AnnaMarburger/SketchingWithHardware/birdbooth_files/schaltplan.png

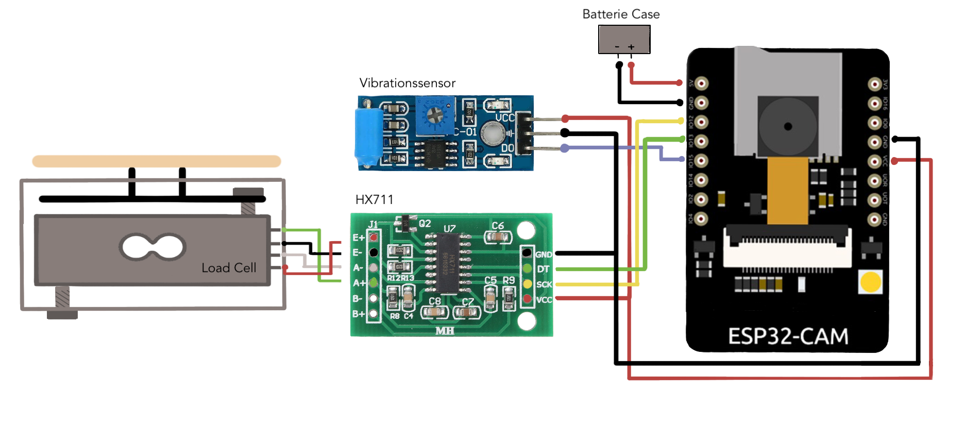
birdbooth_files/schaltplan.png
