AnnaMarburger/SketchingWithHardware/content/posts/media/infoschild.png

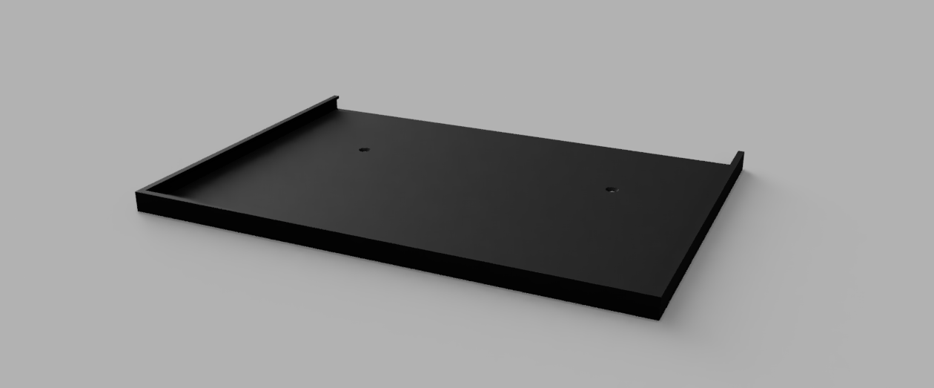
content/posts/media/infoschild.png
