AnnaMarburger/SketchingWithHardware/content/posts/media/lab4_qboydruck.jpeg

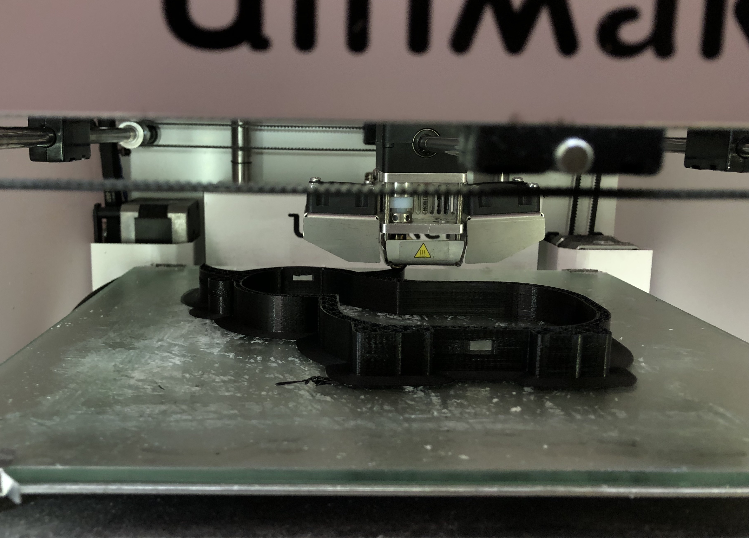
content/posts/media/lab4_qboydruck.jpeg
