AnnaMarburger/SketchingWithHardware/content/posts/media/mech_3gang_1.jpeg

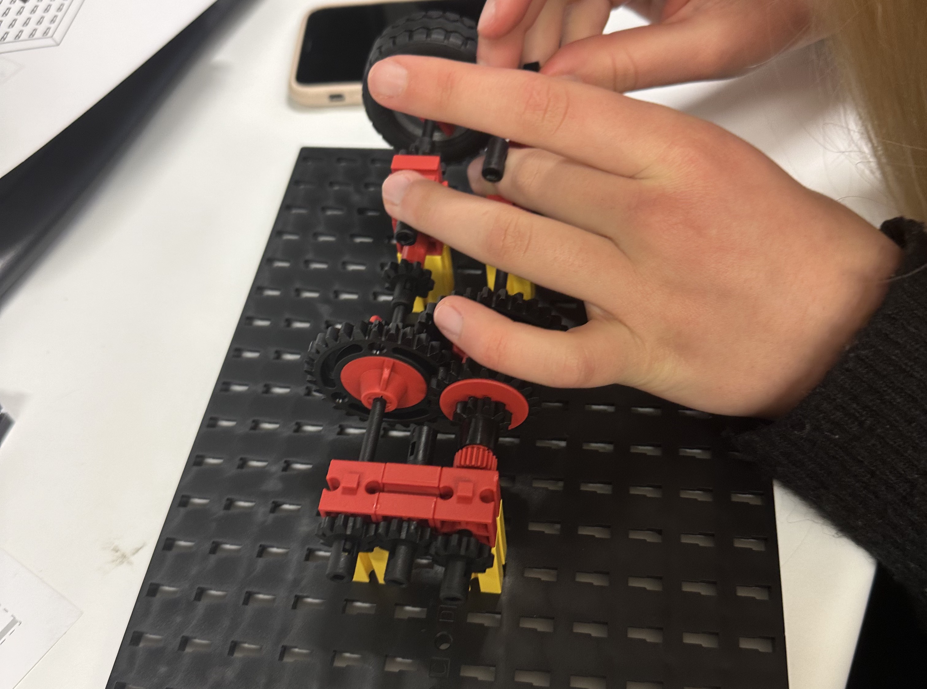
content/posts/media/mech_3gang_1.jpeg
