AnnaMarburger/SketchingWithHardware/content/posts/media/mech_getriebe.jpeg

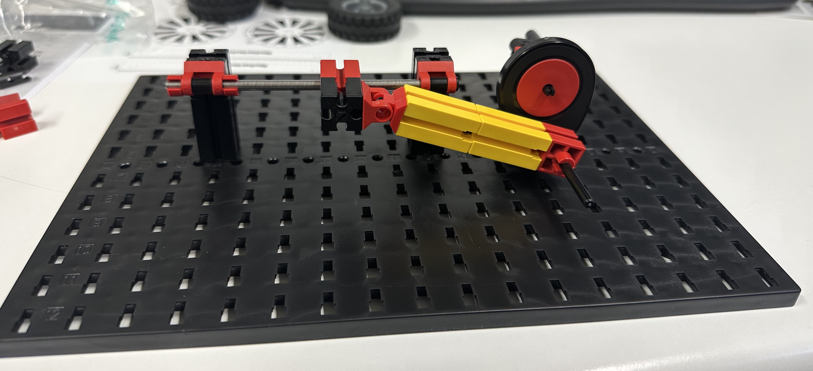
content/posts/media/mech_getriebe.jpeg
