AnnaMarburger/SketchingWithHardware/content/posts/media/mech_titel.jpeg

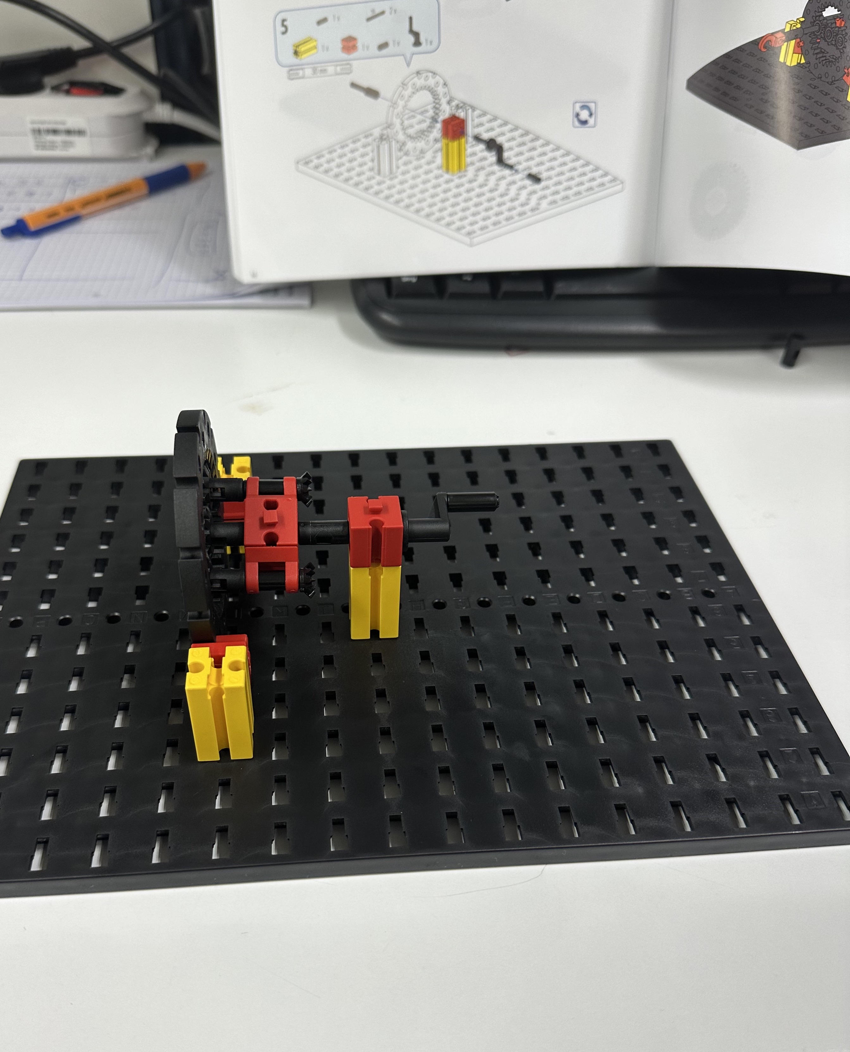
content/posts/media/mech_titel.jpeg
