AnnaMarburger/SketchingWithHardware/content/posts/media/projekt/ablaufdiagramm.png

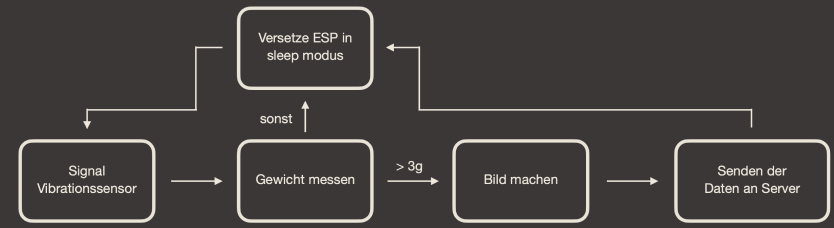
content/posts/media/projekt/ablaufdiagramm.png
