AnnaMarburger/SketchingWithHardware/content/posts/media/projekt/bauteile_gewichtssensor.jpeg

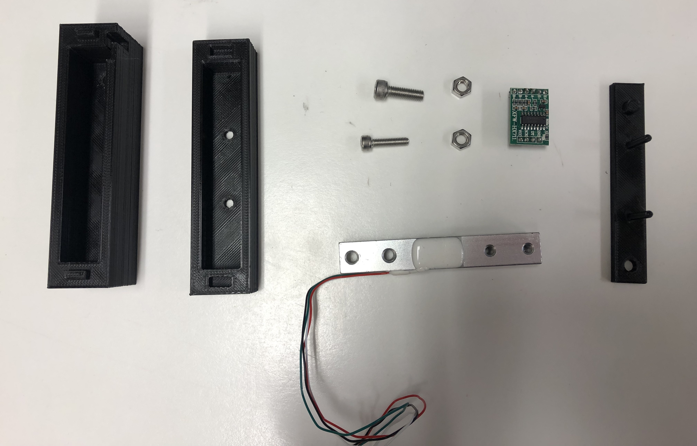
content/posts/media/projekt/bauteile_gewichtssensor.jpeg
