AnnaMarburger/SketchingWithHardware/content/posts/media/projekt/dachplatte.jpeg

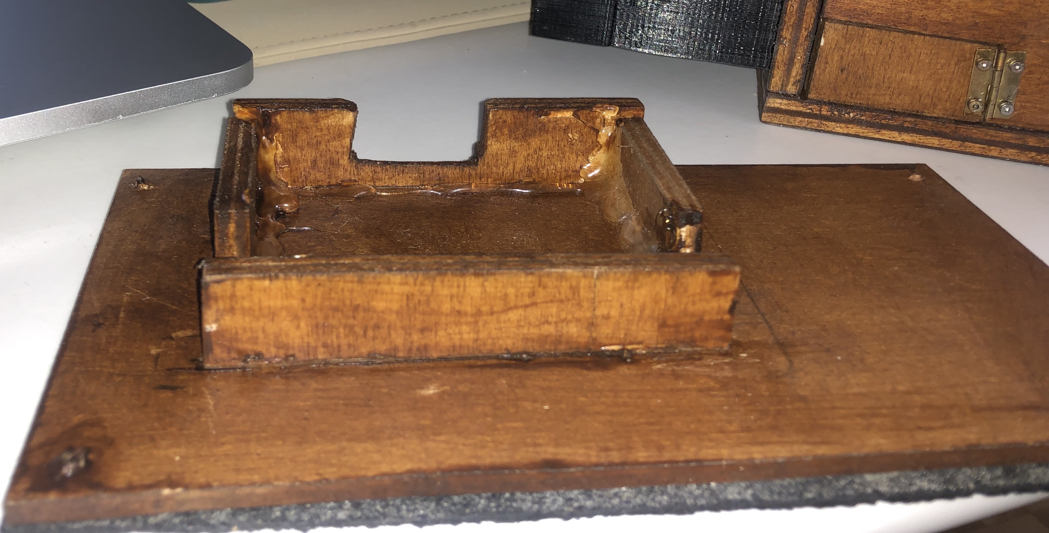
content/posts/media/projekt/dachplatte.jpeg
