AnnaMarburger/SketchingWithHardware/content/posts/media/projekt/Futterschale_boden.jpeg

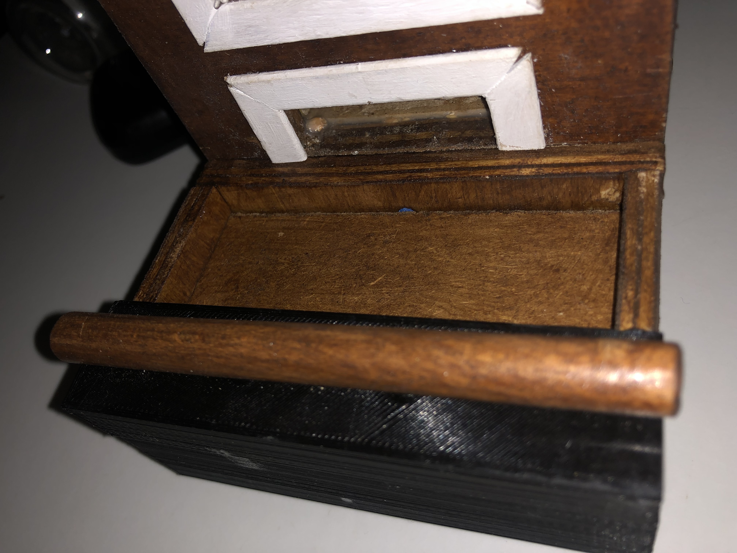
content/posts/media/projekt/Futterschale_boden.jpeg
