AnnaMarburger/SketchingWithHardware/content/posts/media/projekt/futterschale_untererTeil.jpeg

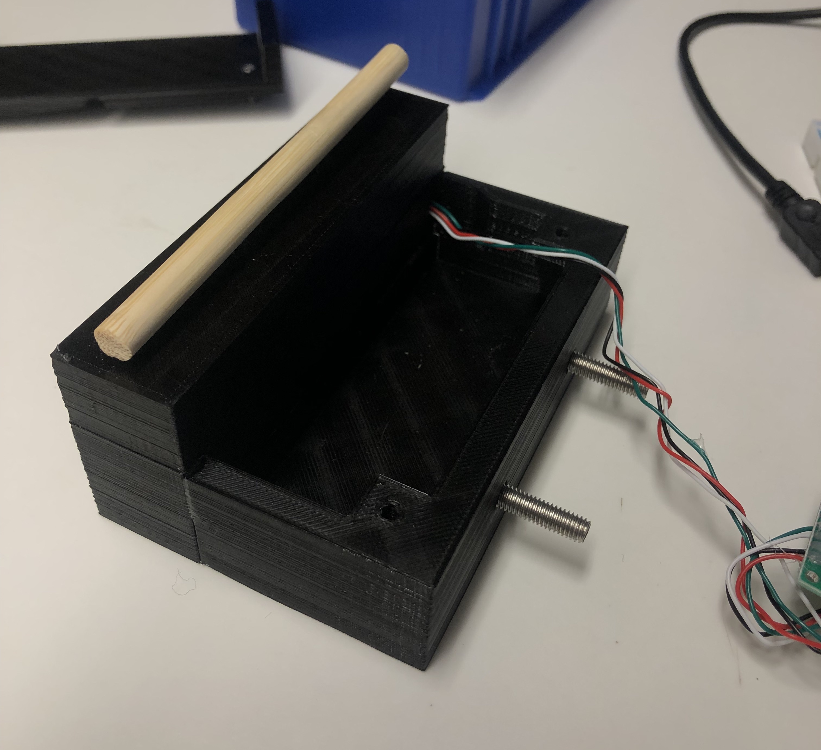
content/posts/media/projekt/futterschale_untererTeil.jpeg
