AnnaMarburger/SketchingWithHardware/content/posts/media/projekt/gewichtssensor.jpeg

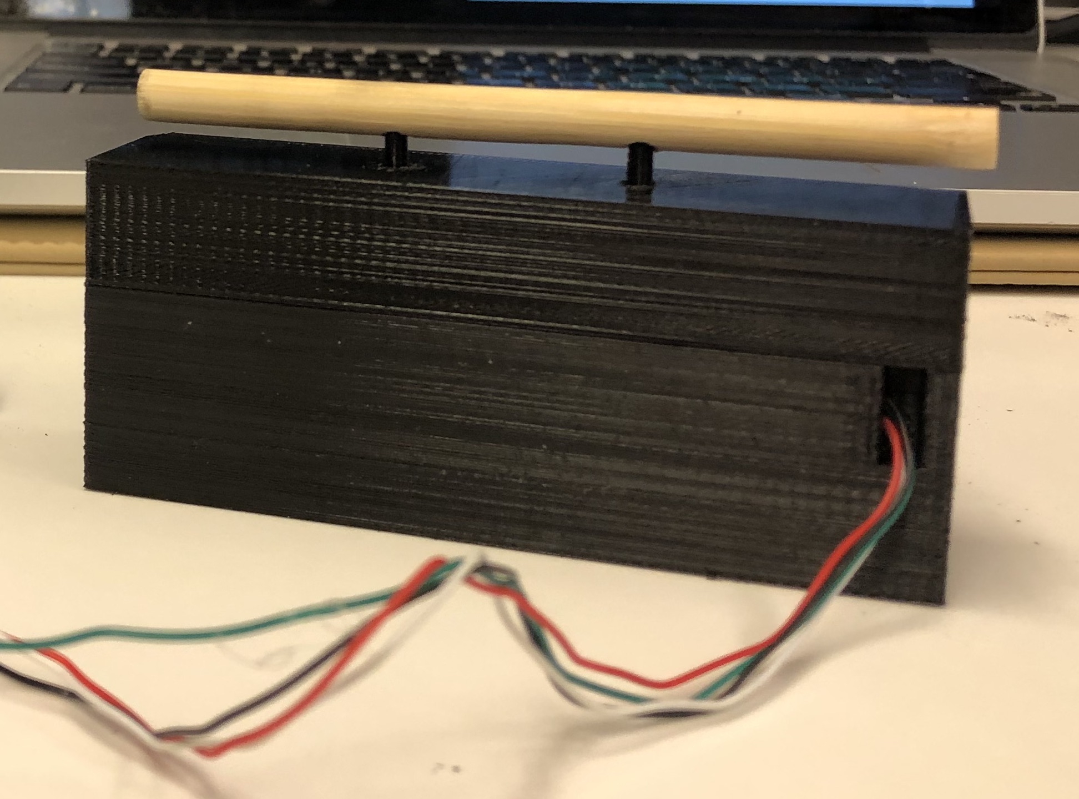
content/posts/media/projekt/gewichtssensor.jpeg
