AnnaMarburger/SketchingWithHardware/content/posts/media/projekt/haus_innen_kabel.jpeg

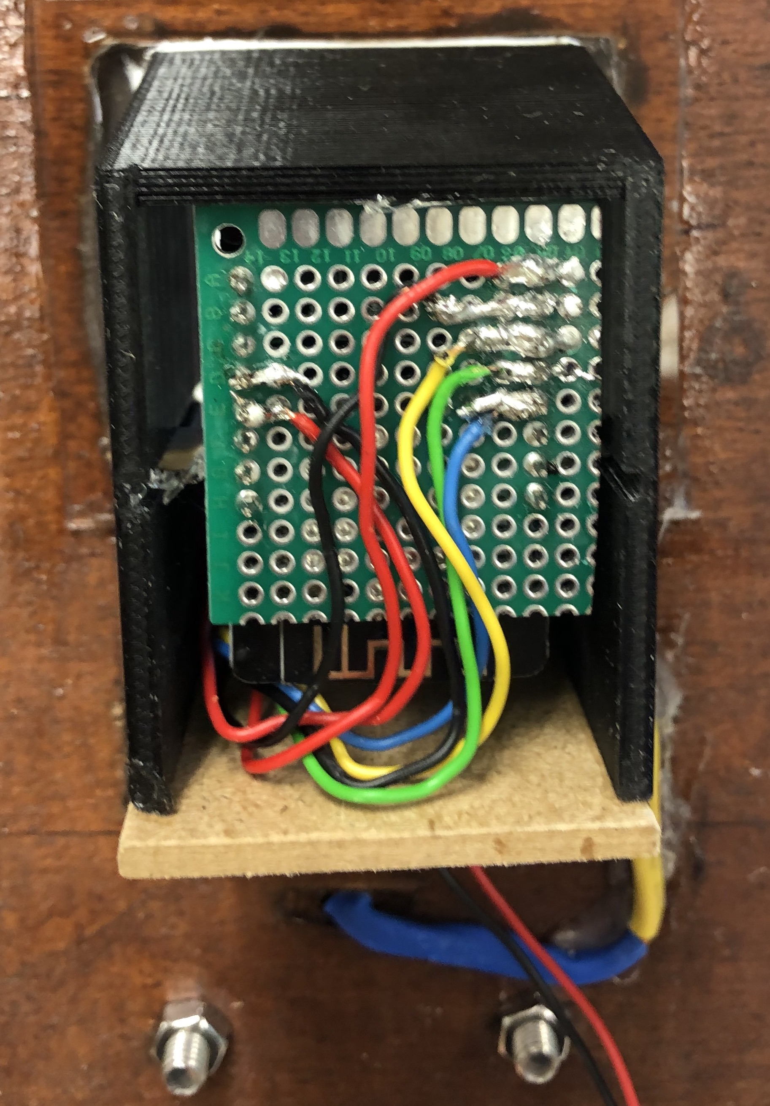
content/posts/media/projekt/haus_innen_kabel.jpeg
