AnnaMarburger/SketchingWithHardware/content/posts/media/projekt/haus_innen_zwischenboden.jpeg

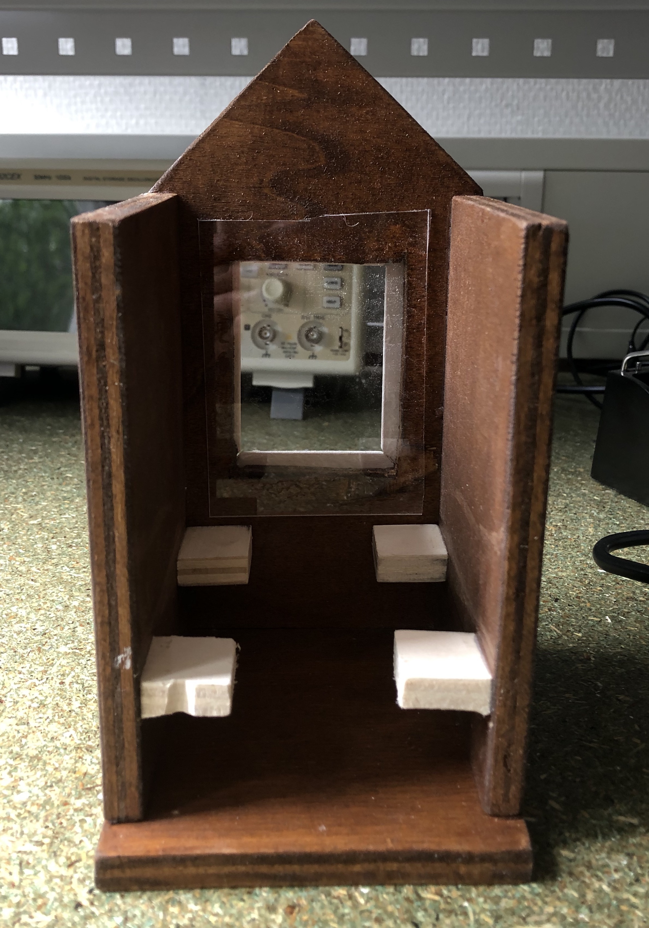
content/posts/media/projekt/haus_innen_zwischenboden.jpeg
