AnnaMarburger/SketchingWithHardware/content/posts/media/projekt/haus_rueckseite.jpeg

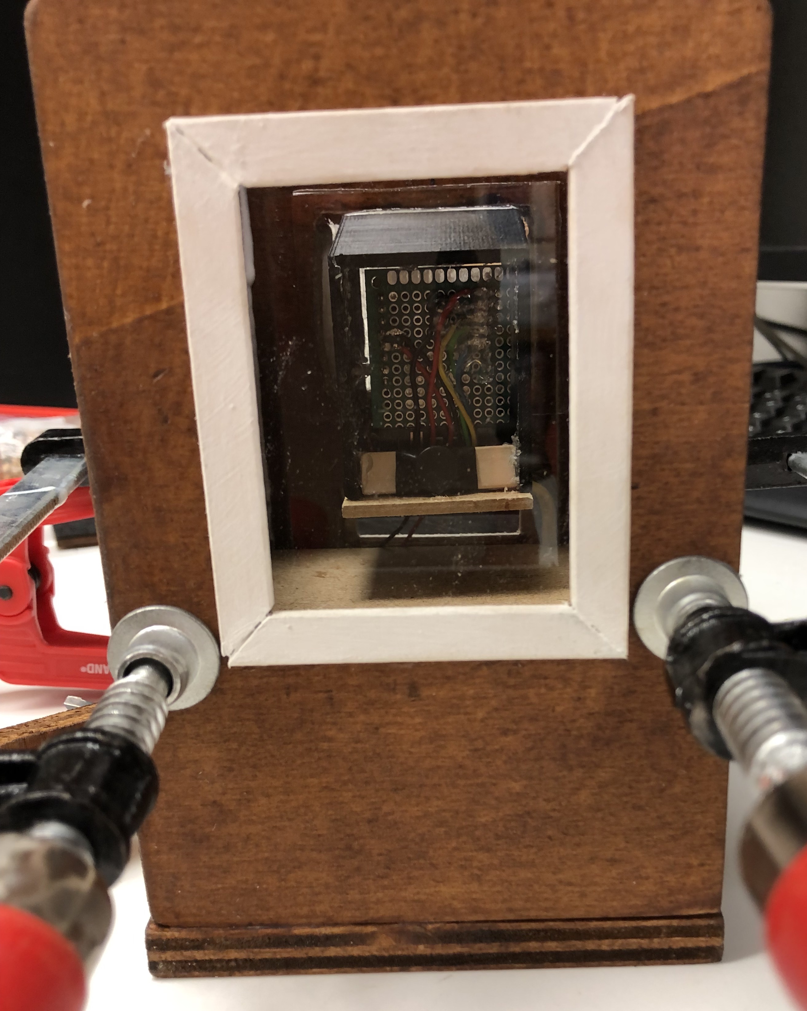
content/posts/media/projekt/haus_rueckseite.jpeg
