AnnaMarburger/SketchingWithHardware/content/posts/media/projekt/haus_vorne.jpeg

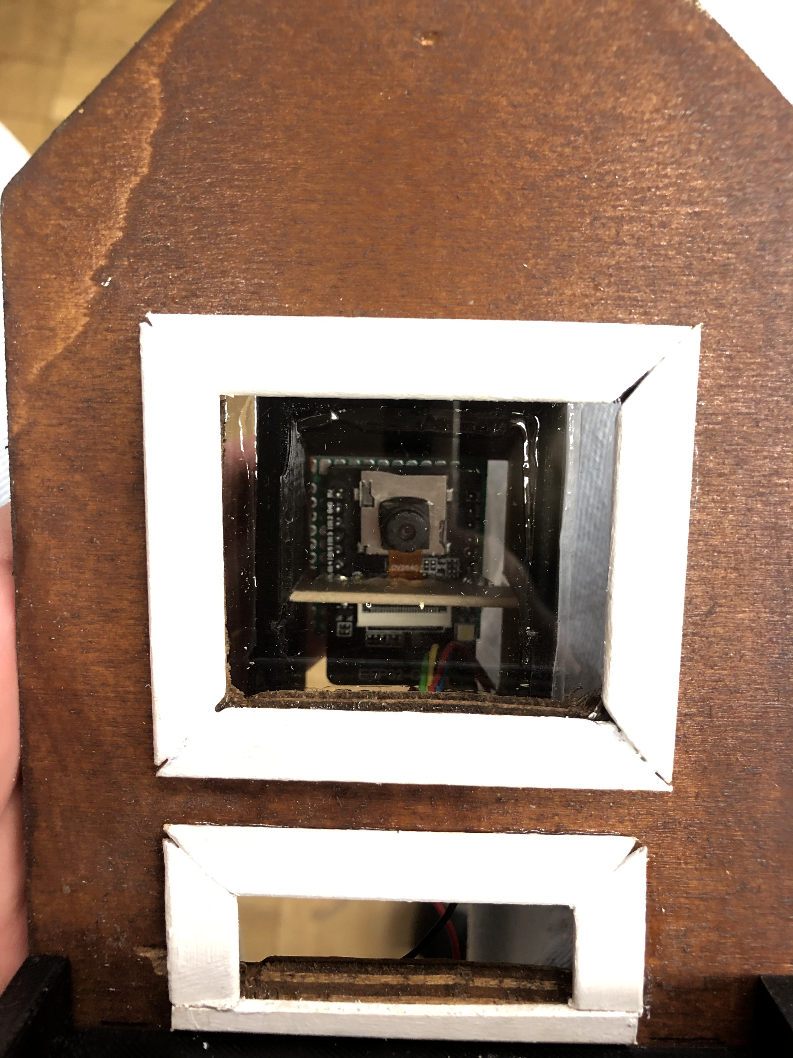
content/posts/media/projekt/haus_vorne.jpeg
