AnnaMarburger/SketchingWithHardware/content/posts/media/projekt/keller.jpeg

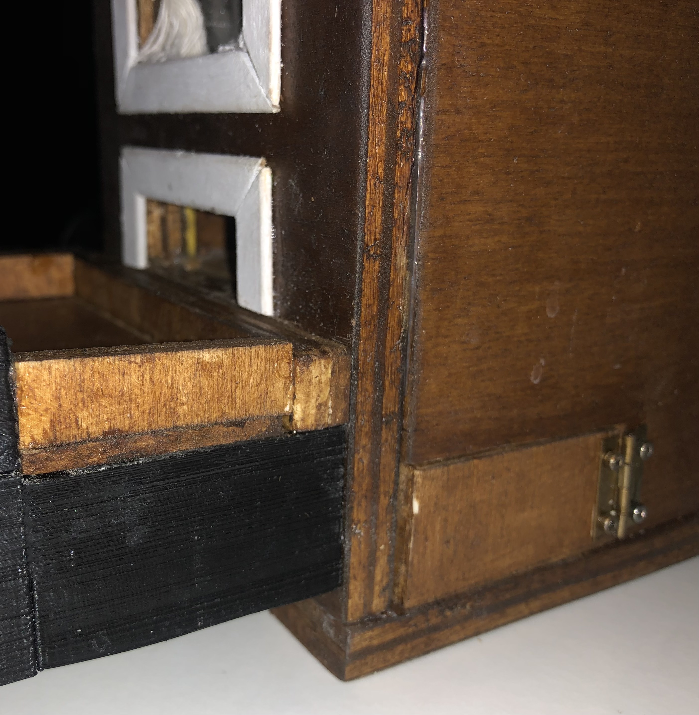
content/posts/media/projekt/keller.jpeg
