AnnaMarburger/SketchingWithHardware/content/posts/media/projekt/modell_sensorcaseoben.png

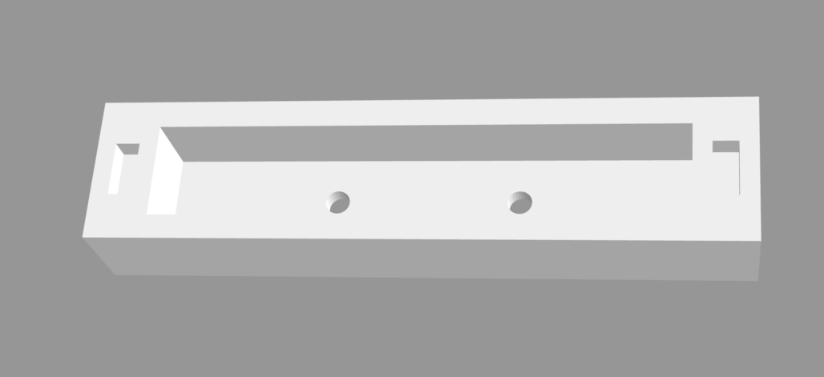
content/posts/media/projekt/modell_sensorcaseoben.png
