AnnaMarburger/SketchingWithHardware/content/posts/media/projekt/modell_sensorcaseunten.png

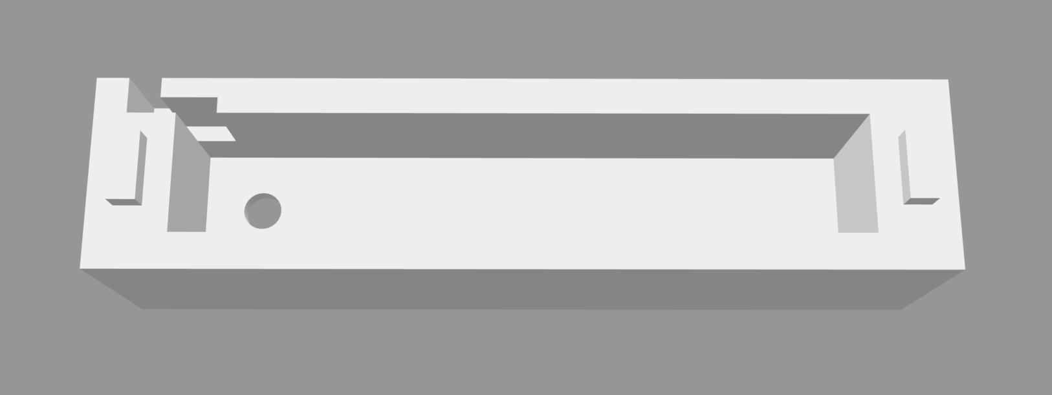
content/posts/media/projekt/modell_sensorcaseunten.png
