AnnaMarburger/SketchingWithHardware/content/posts/media/projekt/modell_waagblatt.png

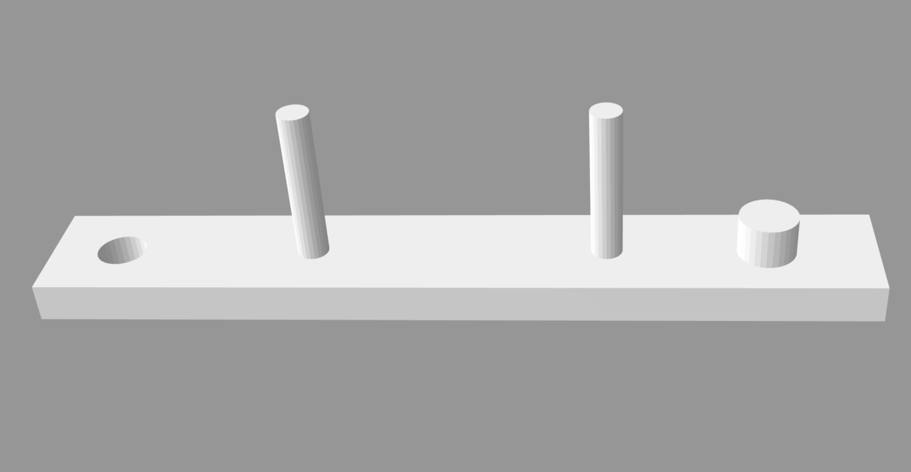
content/posts/media/projekt/modell_waagblatt.png
