AnnaMarburger/SketchingWithHardware/content/posts/media/projekt/postman_request.png

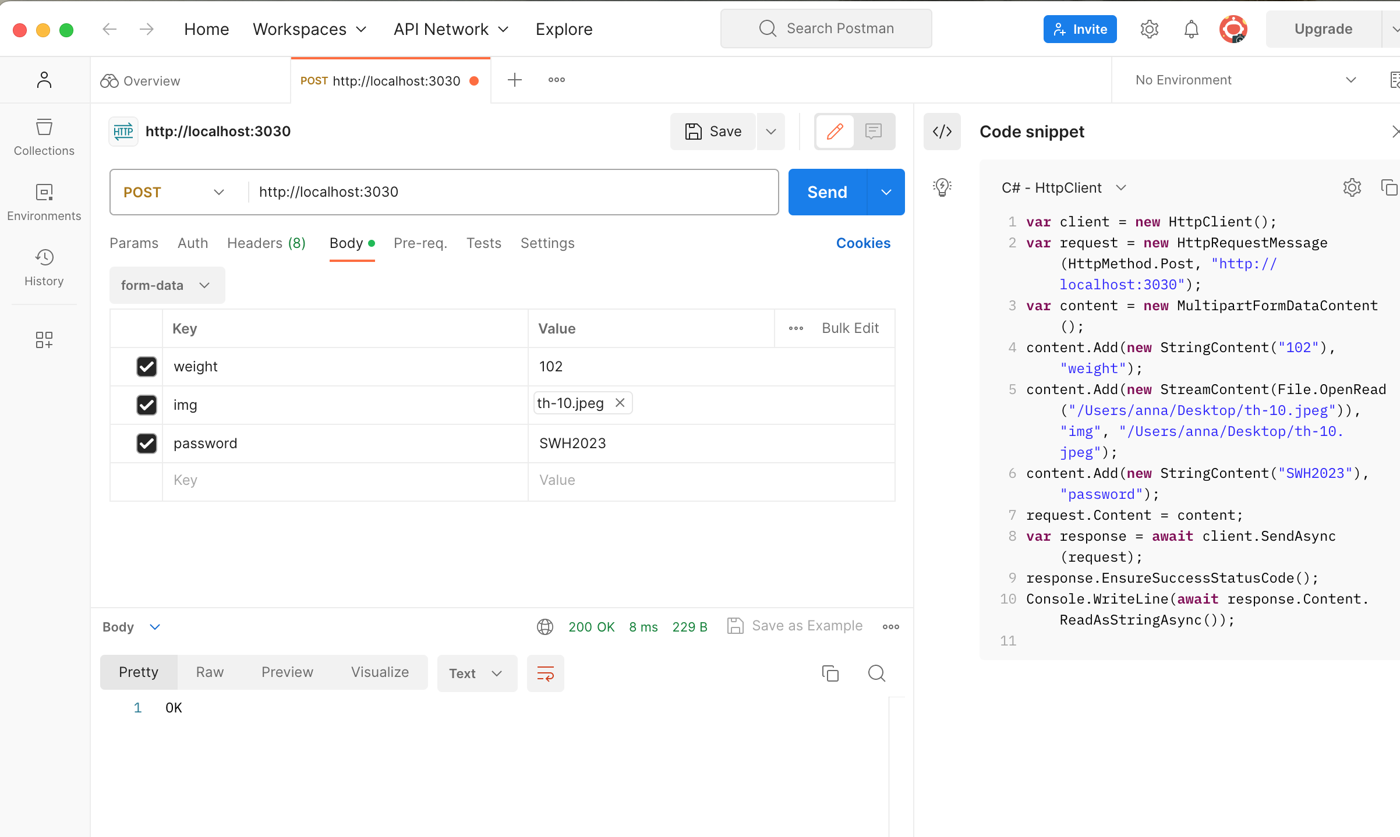
content/posts/media/projekt/postman_request.png
