AnnaMarburger/SketchingWithHardware/content/posts/media/projekt/schaltplan_esp.jpeg

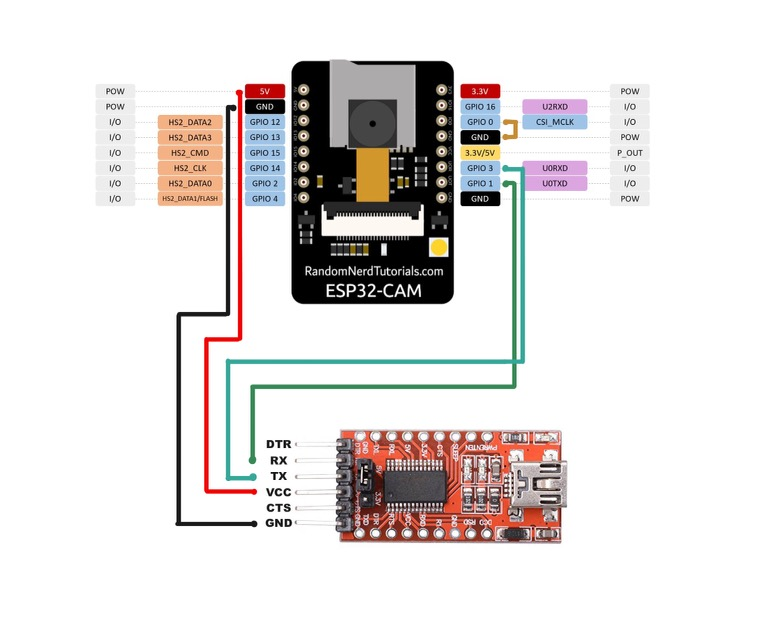
content/posts/media/projekt/schaltplan_esp.jpeg
