AnnaMarburger/SketchingWithHardware/content/posts/media/projekt/schaltplan_loadcell.png

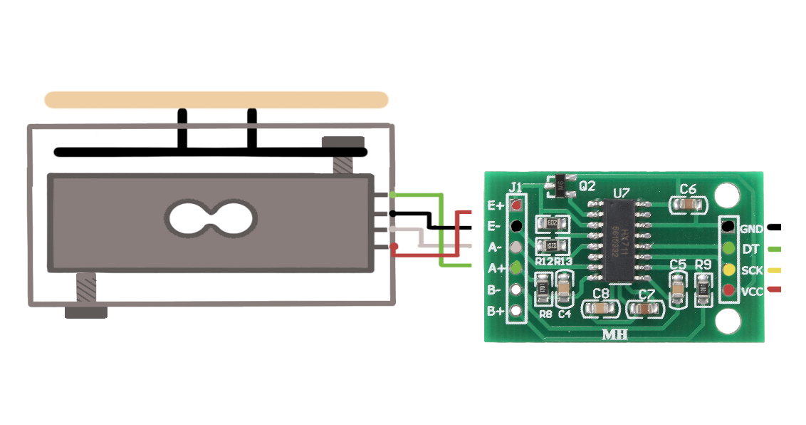
content/posts/media/projekt/schaltplan_loadcell.png
