AnnaMarburger/SketchingWithHardware/content/posts/media/projekt/screen_firebase.png

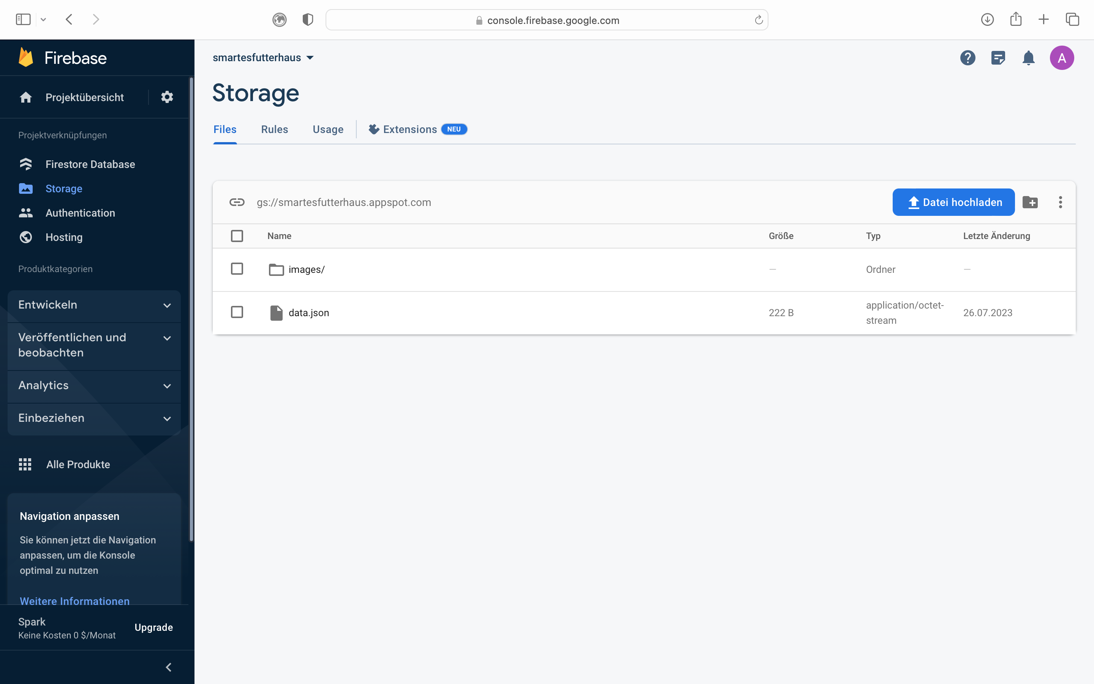
content/posts/media/projekt/screen_firebase.png
