AnnaMarburger/SketchingWithHardware/content/posts/media/projekt/select_AIThinkerCam.png

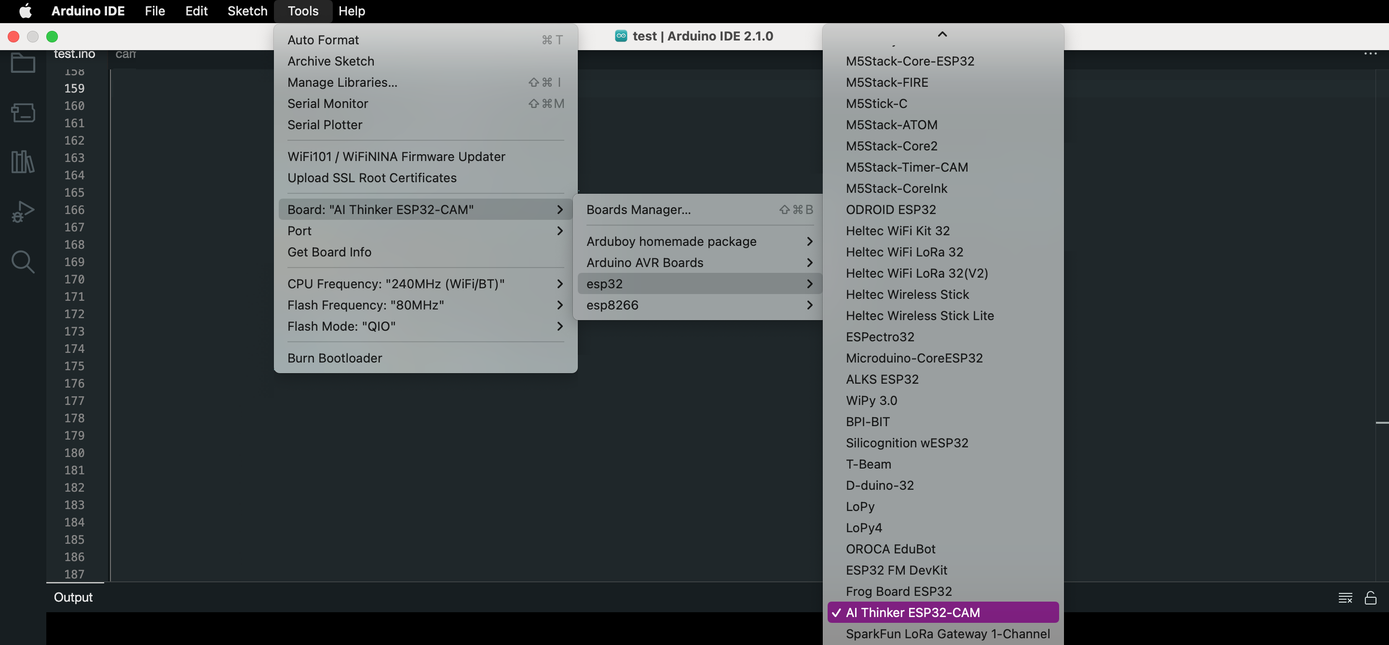
content/posts/media/projekt/select_AIThinkerCam.png
