AnnaMarburger/SketchingWithHardware/content/posts/media/projekt/server_desktop.png

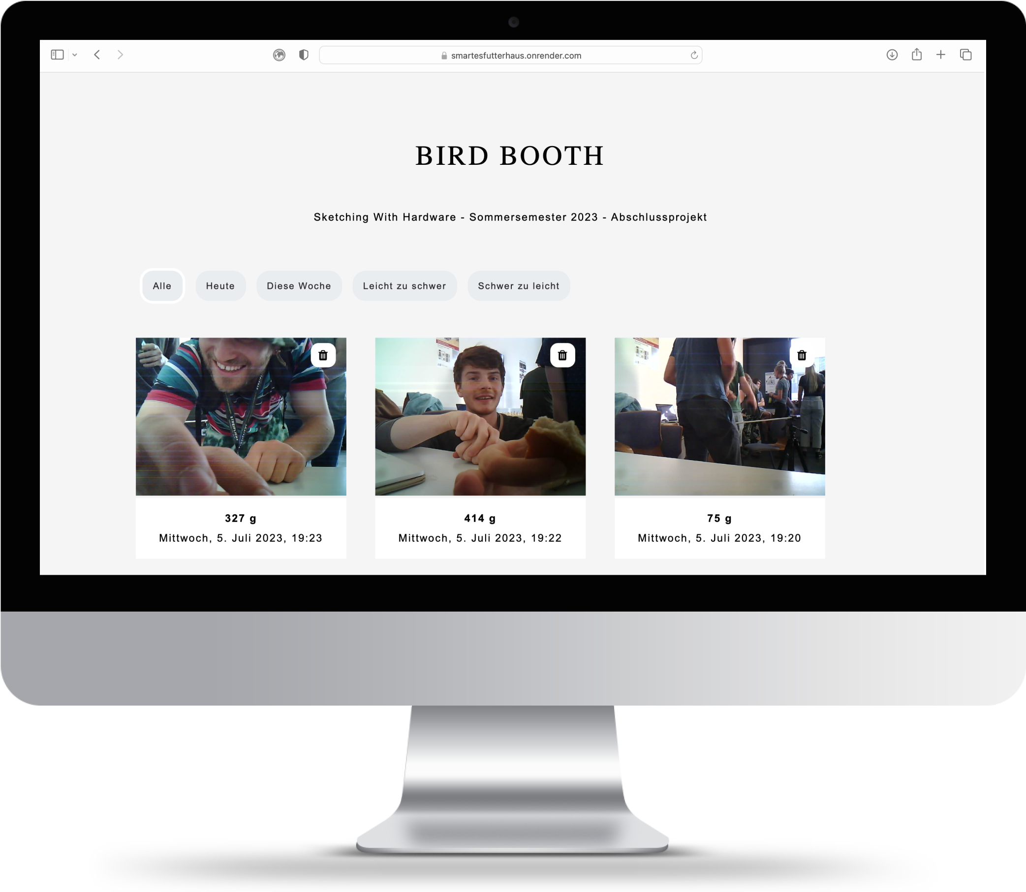
content/posts/media/projekt/server_desktop.png
