AnnaMarburger/SketchingWithHardware/content/posts/media/projekt/server_iphone.png

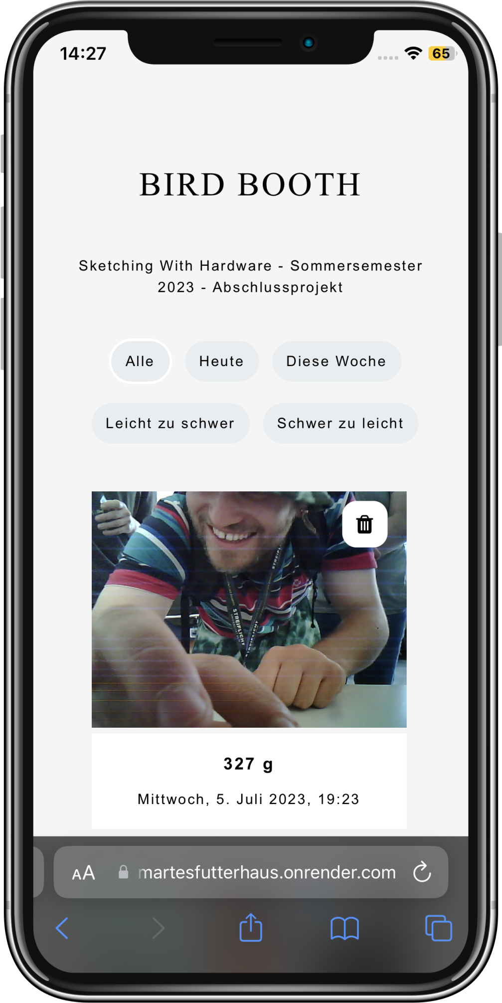
content/posts/media/projekt/server_iphone.png
