AnnaMarburger/SketchingWithHardware/content/posts/media/projekt/steckplatine.jpeg

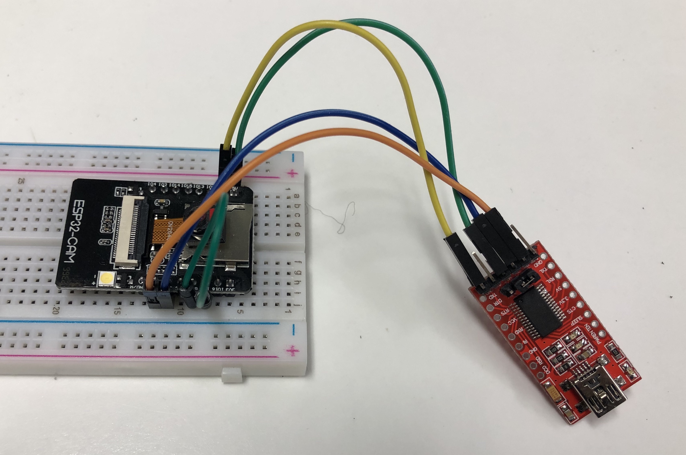
content/posts/media/projekt/steckplatine.jpeg
