AnnaMarburger/SketchingWithHardware/content/posts/media/projekt/zeitplan.png

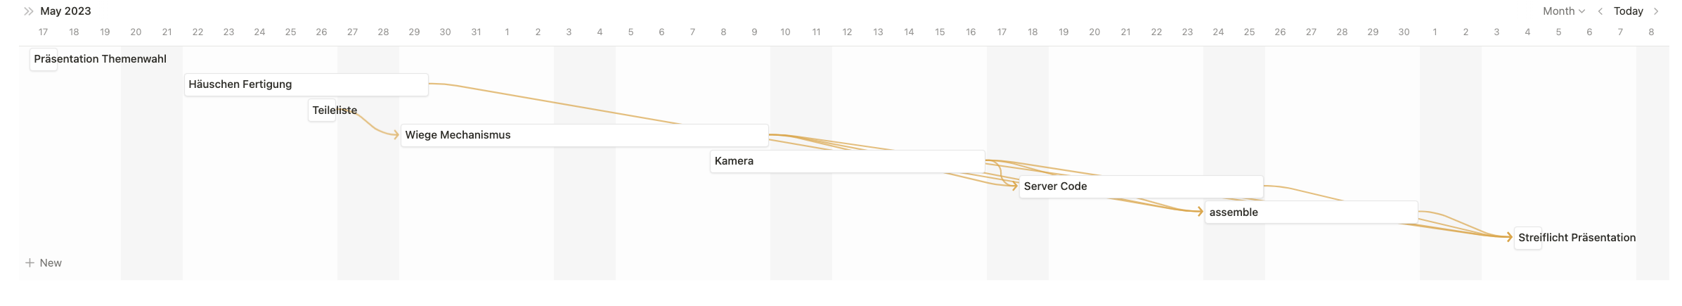
content/posts/media/projekt/zeitplan.png
