AnnaMarburger/SketchingWithHardware/content/posts/media/qboy1.jpeg

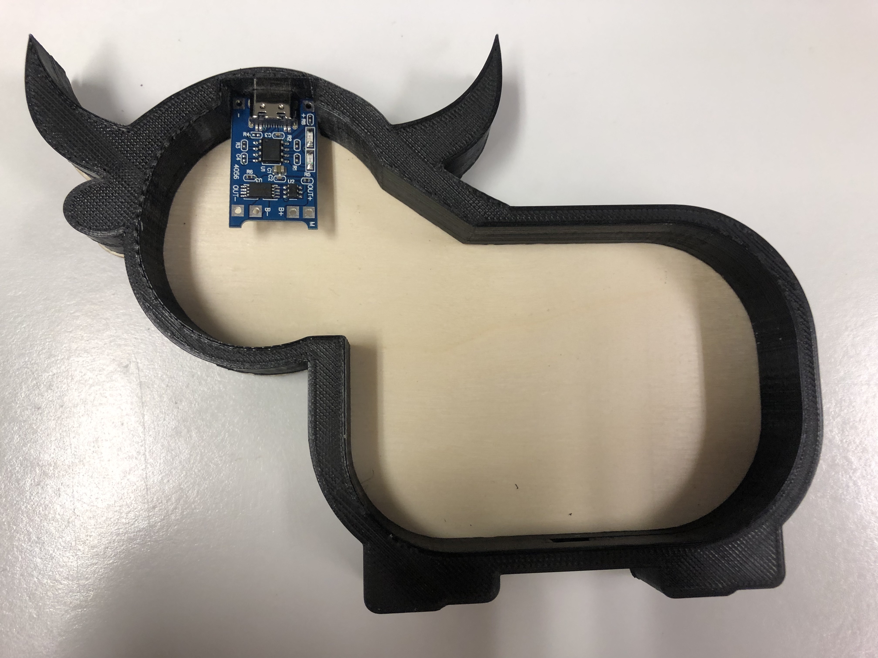
content/posts/media/qboy1.jpeg
