AnnaMarburger/SketchingWithHardware/content/posts/media/qboy2.jpeg

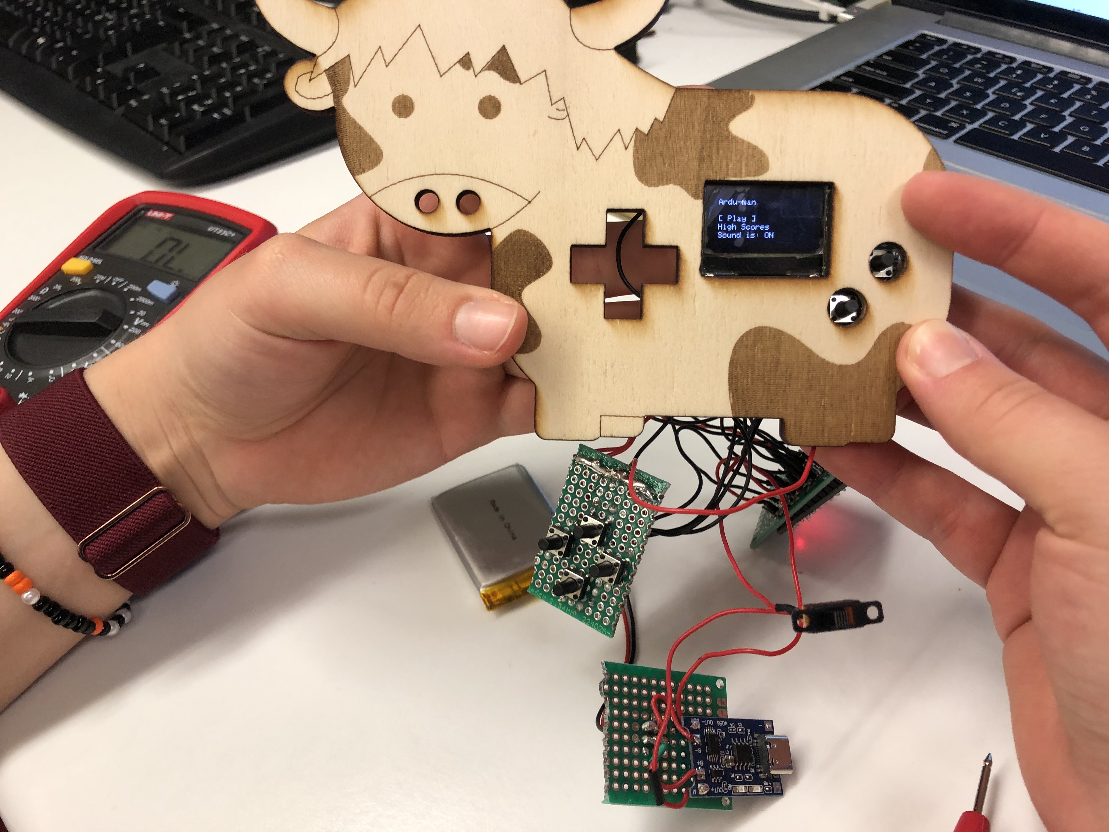
content/posts/media/qboy2.jpeg
