AnnaMarburger/SketchingWithHardware/content/posts/media/qboy_steckbrett.jpeg

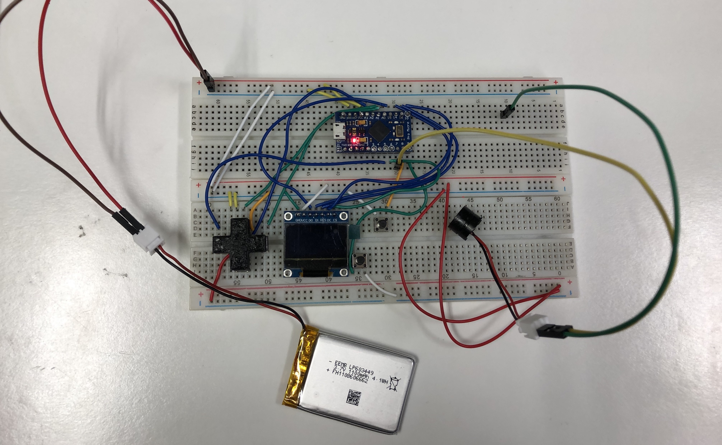
content/posts/media/qboy_steckbrett.jpeg
