AnnaMarburger/SketchingWithHardware/content/posts/media/qboydeckel.jpeg

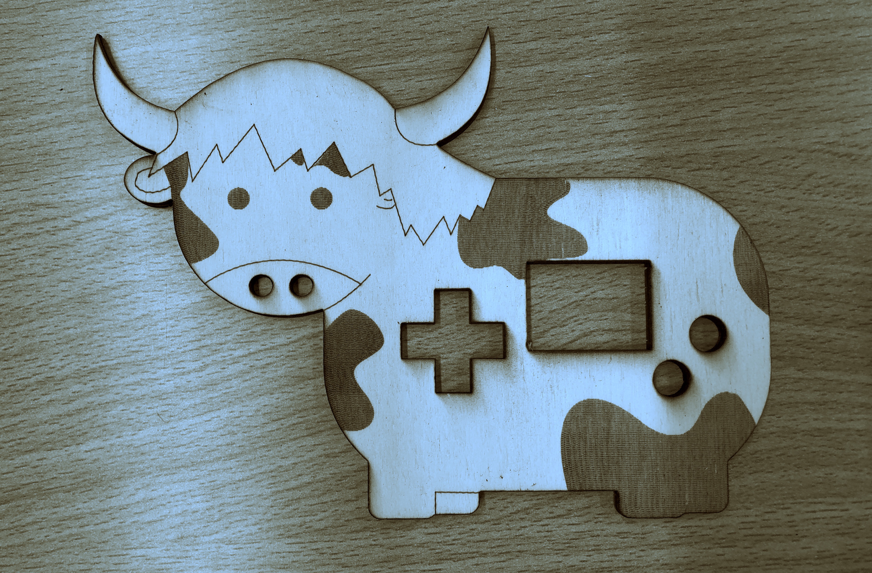
content/posts/media/qboydeckel.jpeg
