AnnaMarburger/SketchingWithHardware/static/media/fertigeshaus.jpg

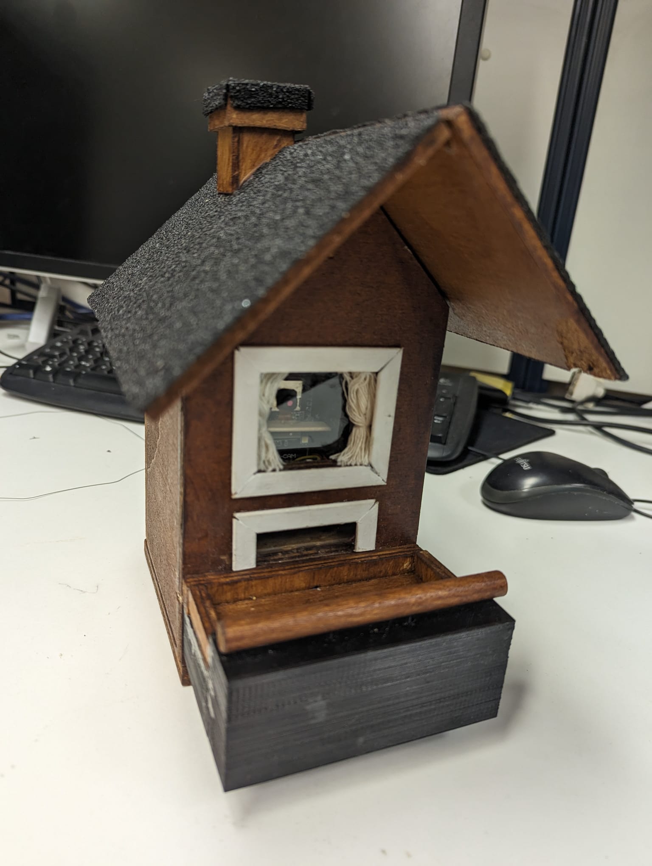
static/media/fertigeshaus.jpg
