AnnaMarburger/SketchingWithHardware/static/media/gamestation_loetplan.png

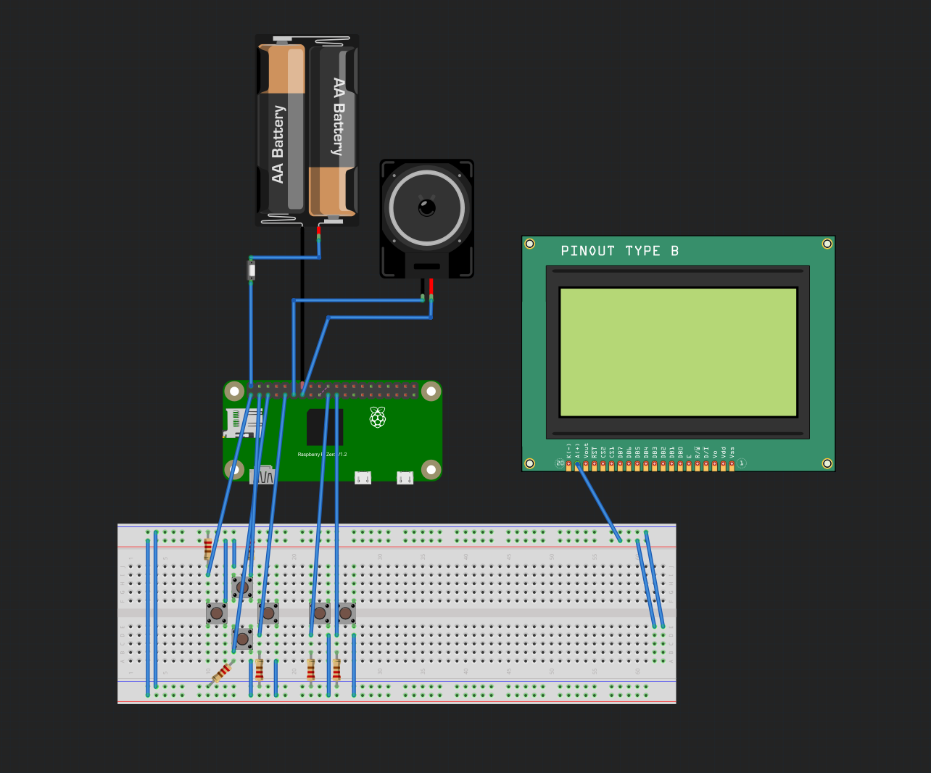
static/media/gamestation_loetplan.png
