AnnaMarburger/SketchingWithHardware/static/media/gamestation_skizze.png

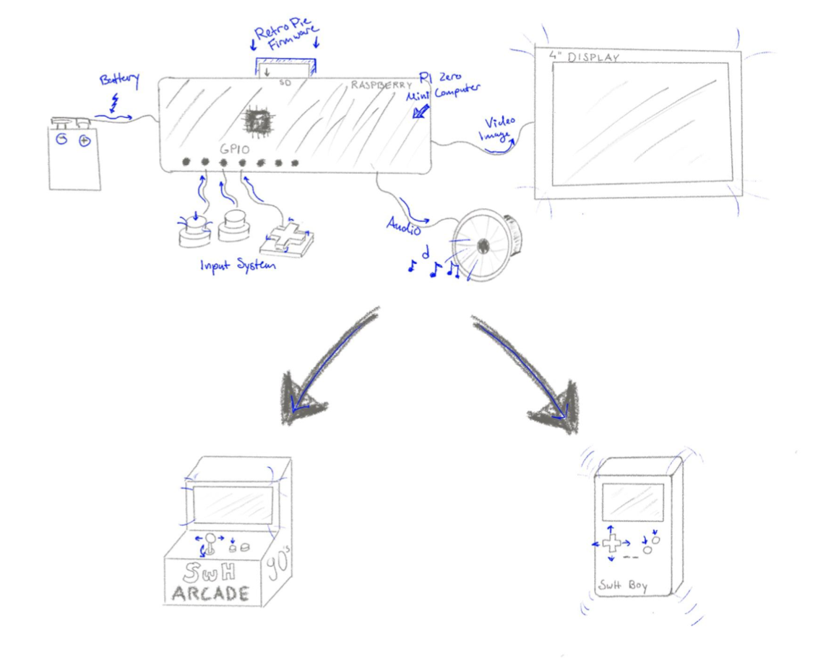
static/media/gamestation_skizze.png
