AnnaMarburger/SketchingWithHardware/static/media/haus_drawing.png

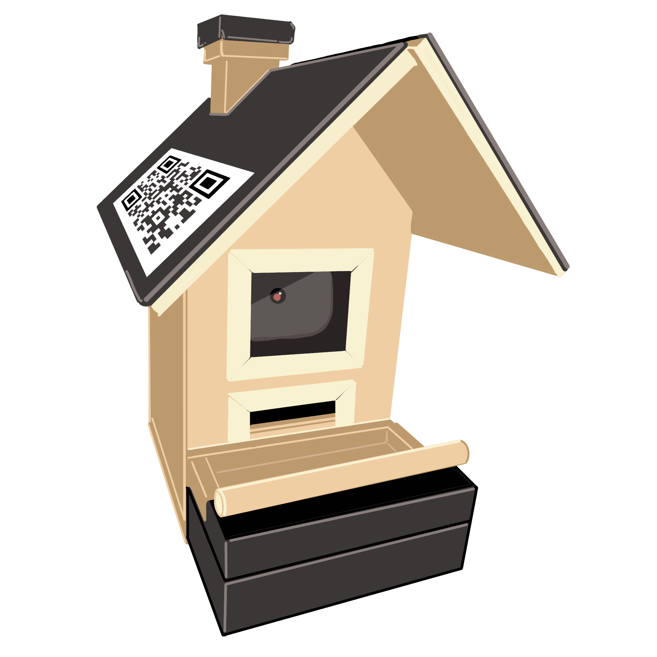
static/media/haus_drawing.png
