AnnaMarburger/SketchingWithHardware/static/media/haus_innen_cam_offen.jpeg

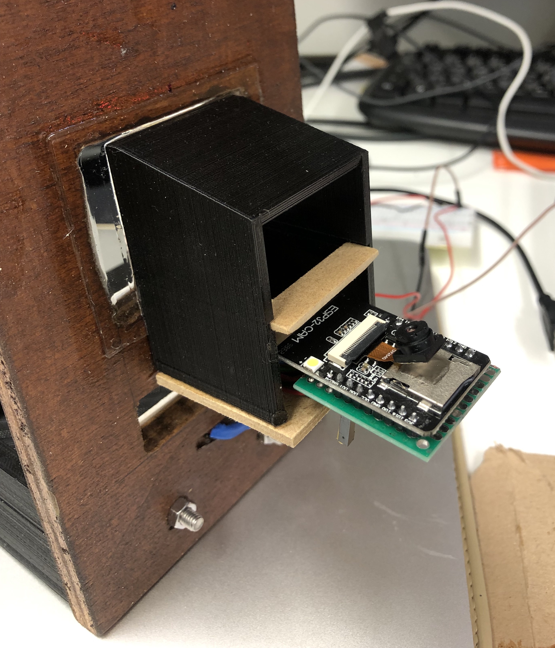
static/media/haus_innen_cam_offen.jpeg
