AnnaMarburger/SketchingWithHardware/static/media/hero.jpeg

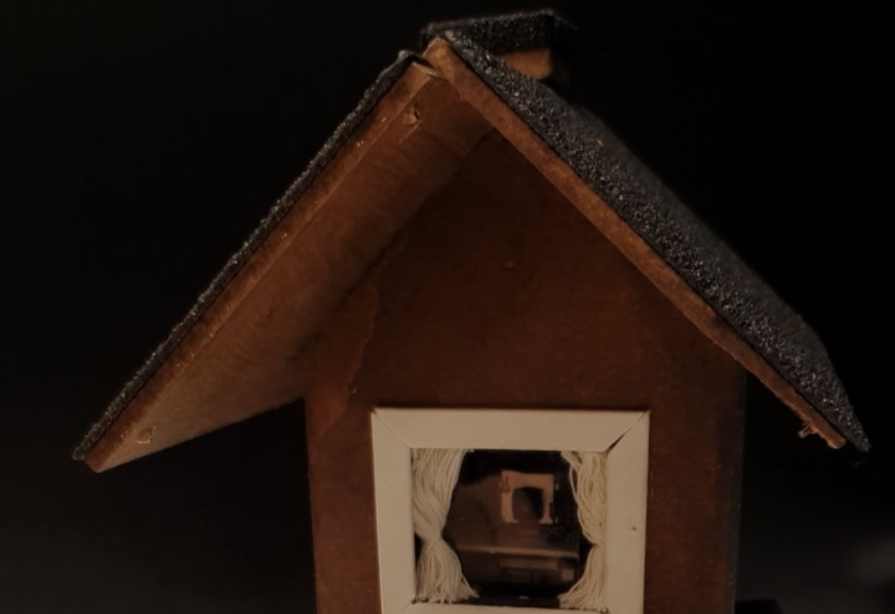
static/media/hero.jpeg
