AnnaMarburger/SketchingWithHardware/static/media/lab1_kennlinie.png

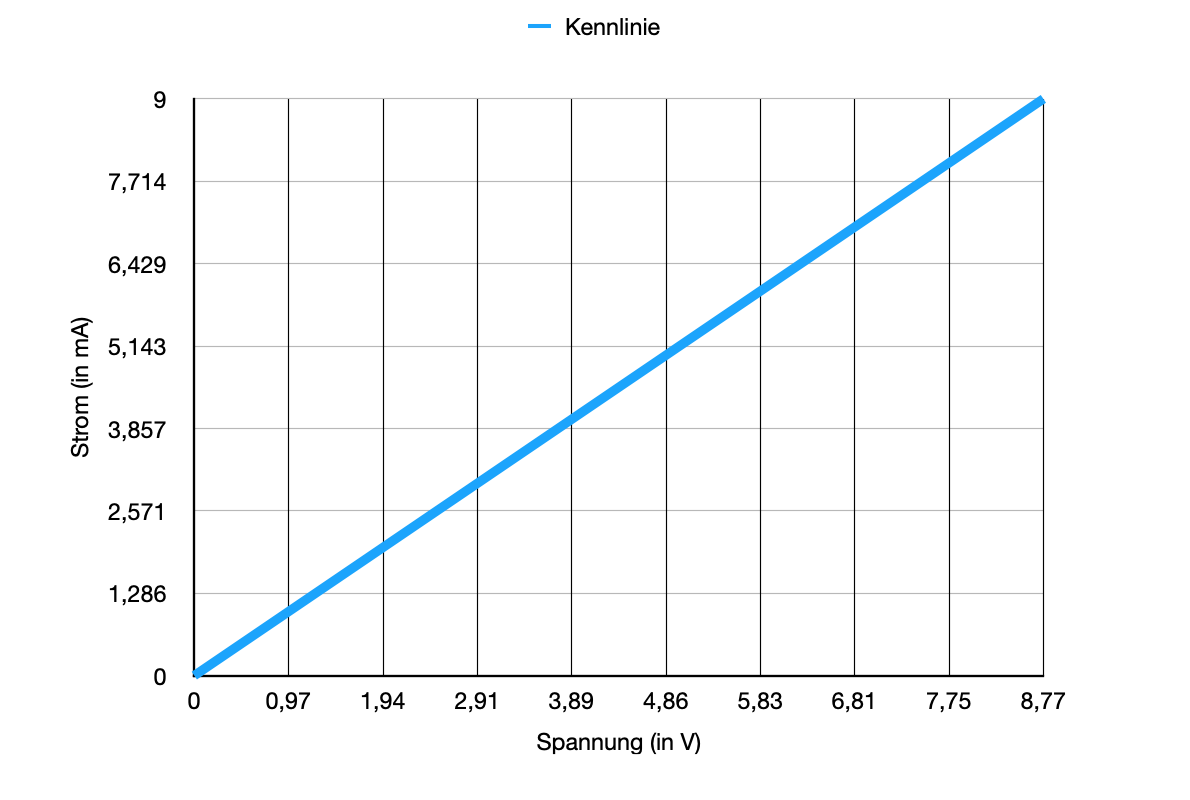
static/media/lab1_kennlinie.png
