AnnaMarburger/SketchingWithHardware/static/media/lab1_messen_schema.png

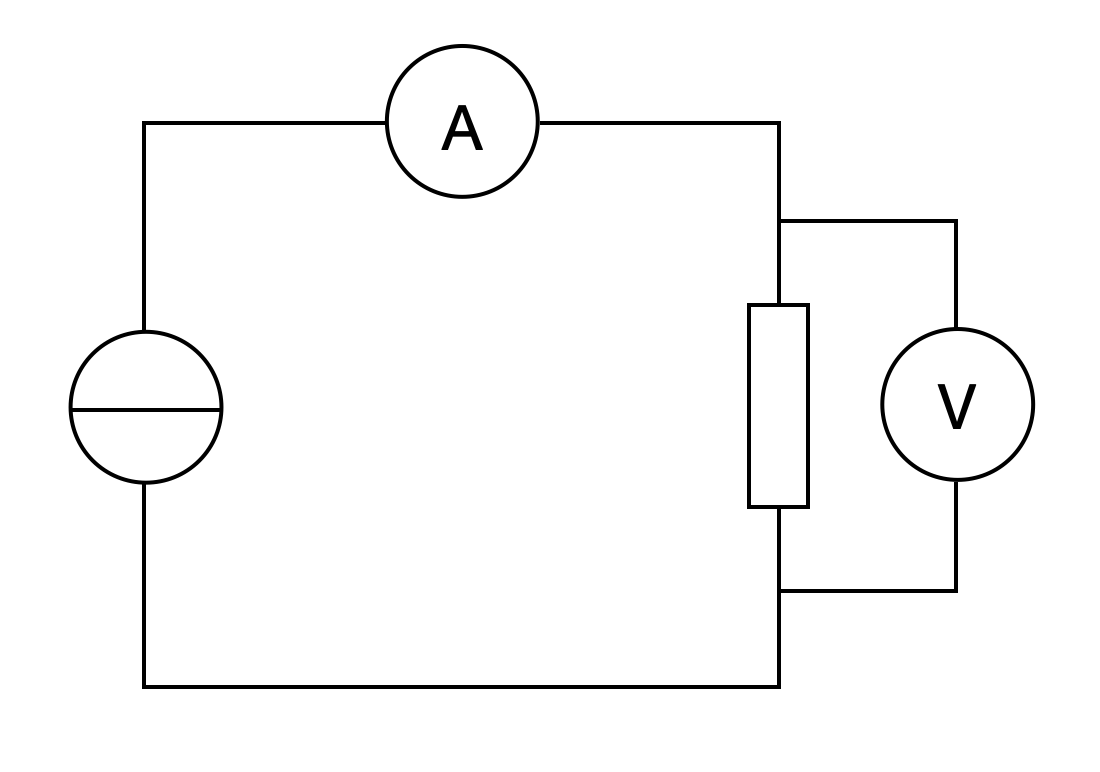
static/media/lab1_messen_schema.png
