AnnaMarburger/SketchingWithHardware/static/media/lab1_messtabelle.png

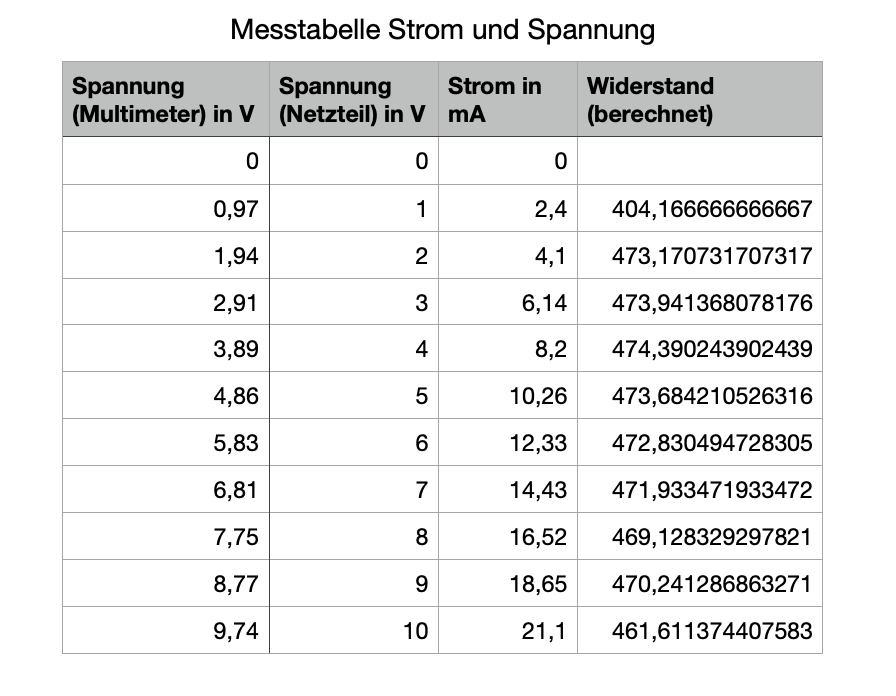
static/media/lab1_messtabelle.png
