AnnaMarburger/SketchingWithHardware/static/media/lab1_spannungsteiler.png

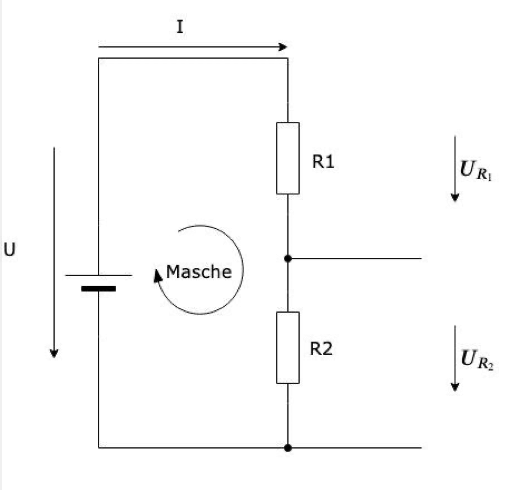
static/media/lab1_spannungsteiler.png
