AnnaMarburger/SketchingWithHardware/static/media/lab2_ledmatrix.jpeg

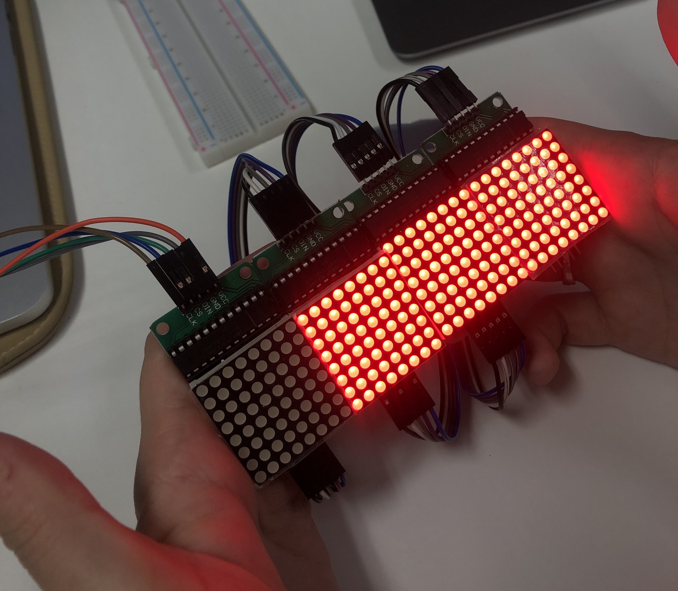
static/media/lab2_ledmatrix.jpeg
