AnnaMarburger/SketchingWithHardware/static/media/lab3_bojackergebnis.jpeg

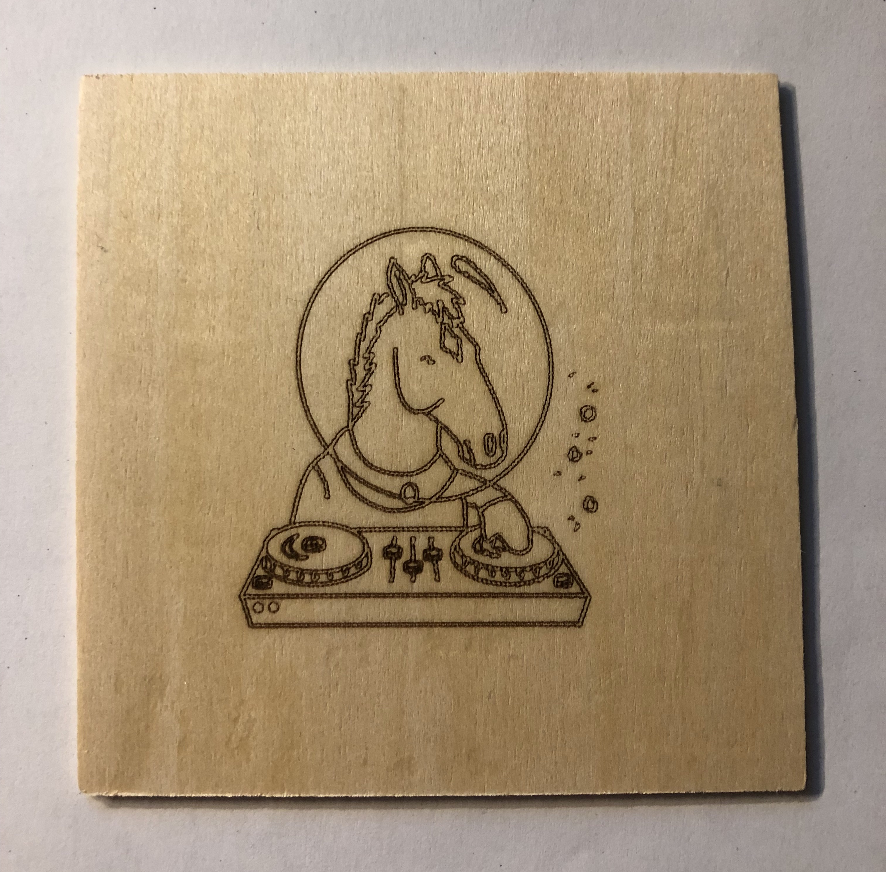
static/media/lab3_bojackergebnis.jpeg
