AnnaMarburger/SketchingWithHardware/static/media/mechanik1.jpeg

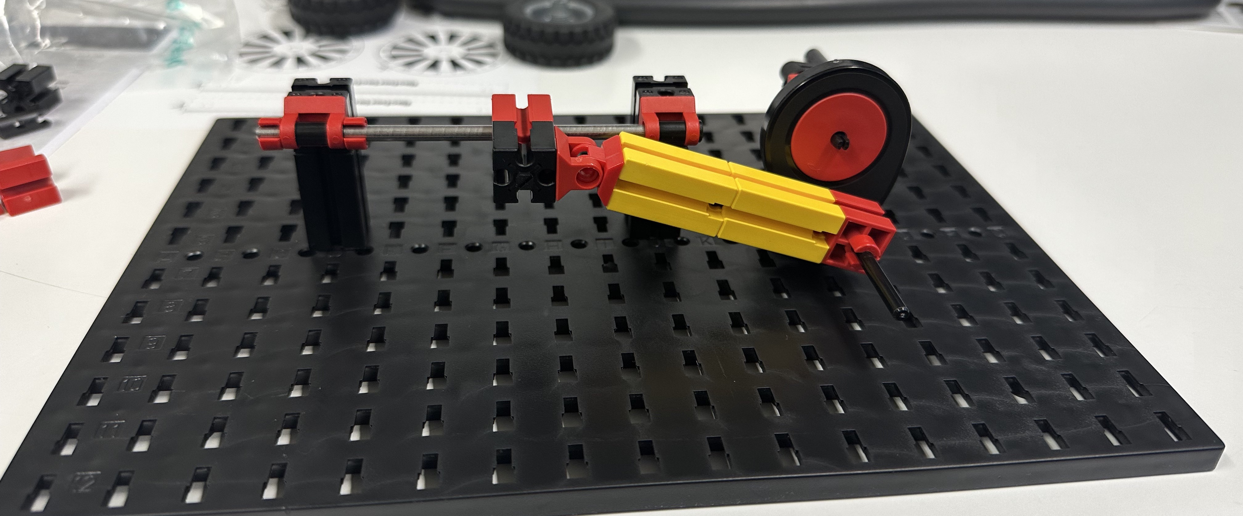
static/media/mechanik1.jpeg
