AnnaMarburger/SketchingWithHardware/static/media/platzhalter.jpeg

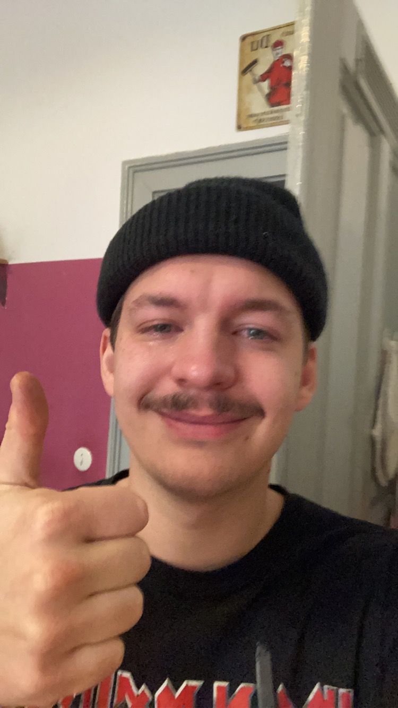
static/media/platzhalter.jpeg
