AnnaMarburger/SketchingWithHardware/static/media/qboy3.jpeg

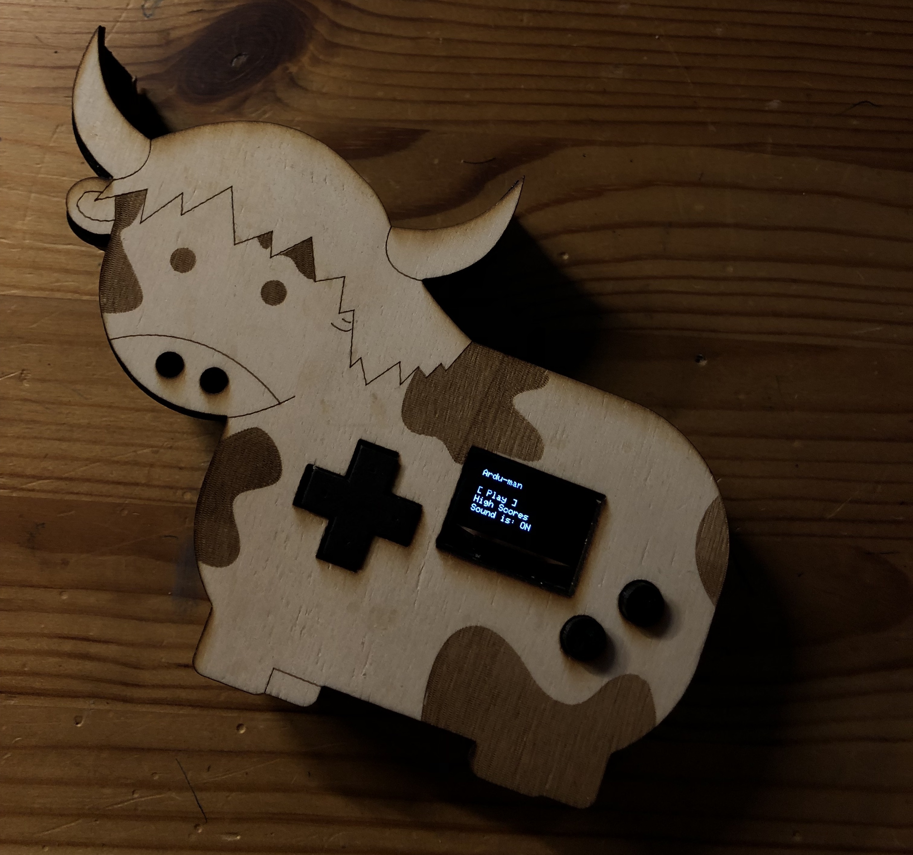
static/media/qboy3.jpeg
