AnnaMarburger/SketchingWithHardware/static/media/QBoySkizze_seite.jpeg

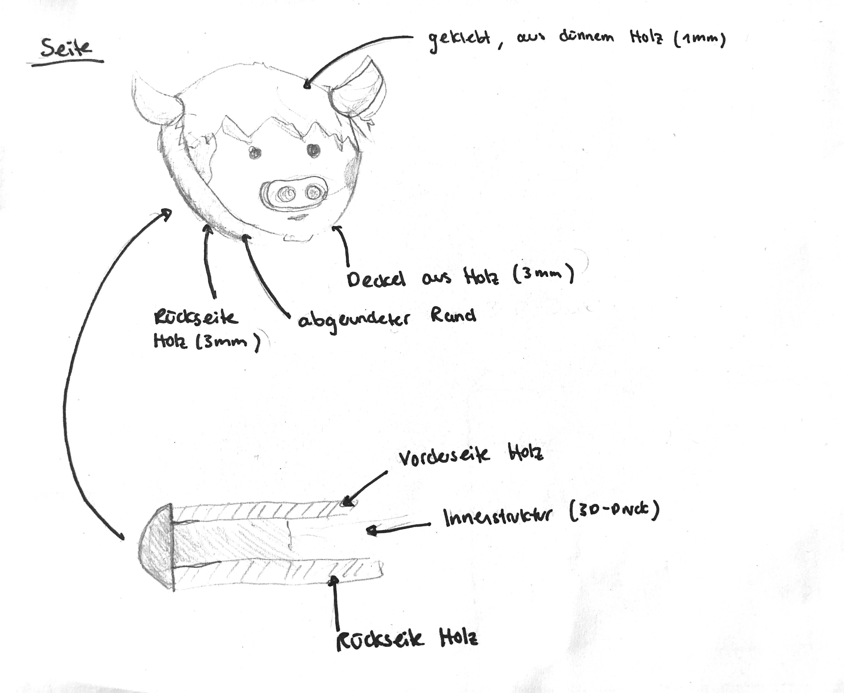
static/media/QBoySkizze_seite.jpeg
