AnnaMarburger/SketchingWithHardware/static/media/QBoySkizze_vorne.jpeg

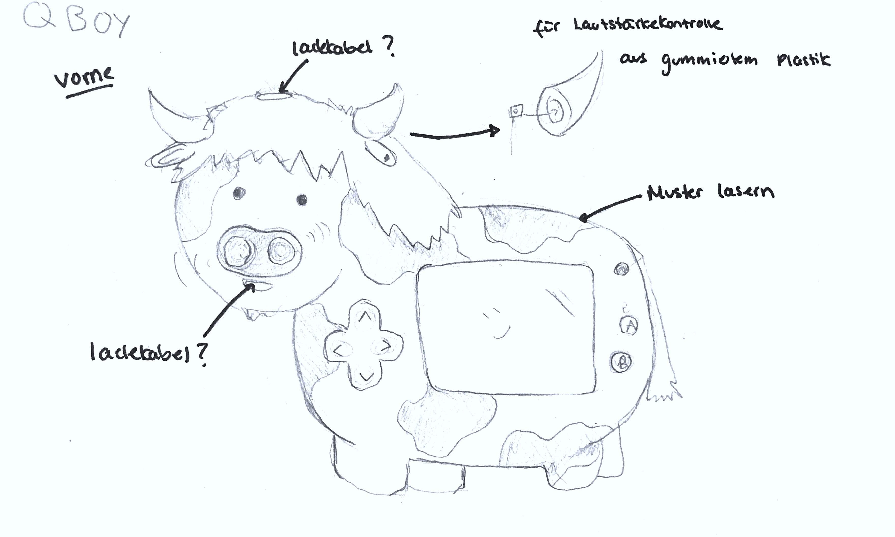
static/media/QBoySkizze_vorne.jpeg
