AnnaMarburger/SketchingWithHardware/content/posts/media/projekt/haus_innen_cam.jpeg

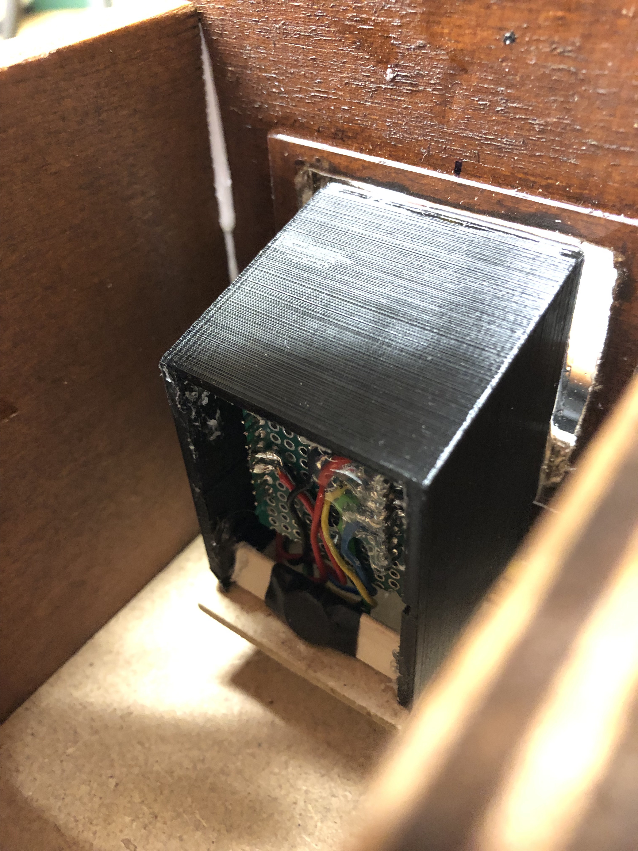
content/posts/media/projekt/haus_innen_cam.jpeg
